fau-fablab/uacs-hardware/pcb/uacs.sch

## EAGLE design pcb/uacs.sch (2014-12-10)

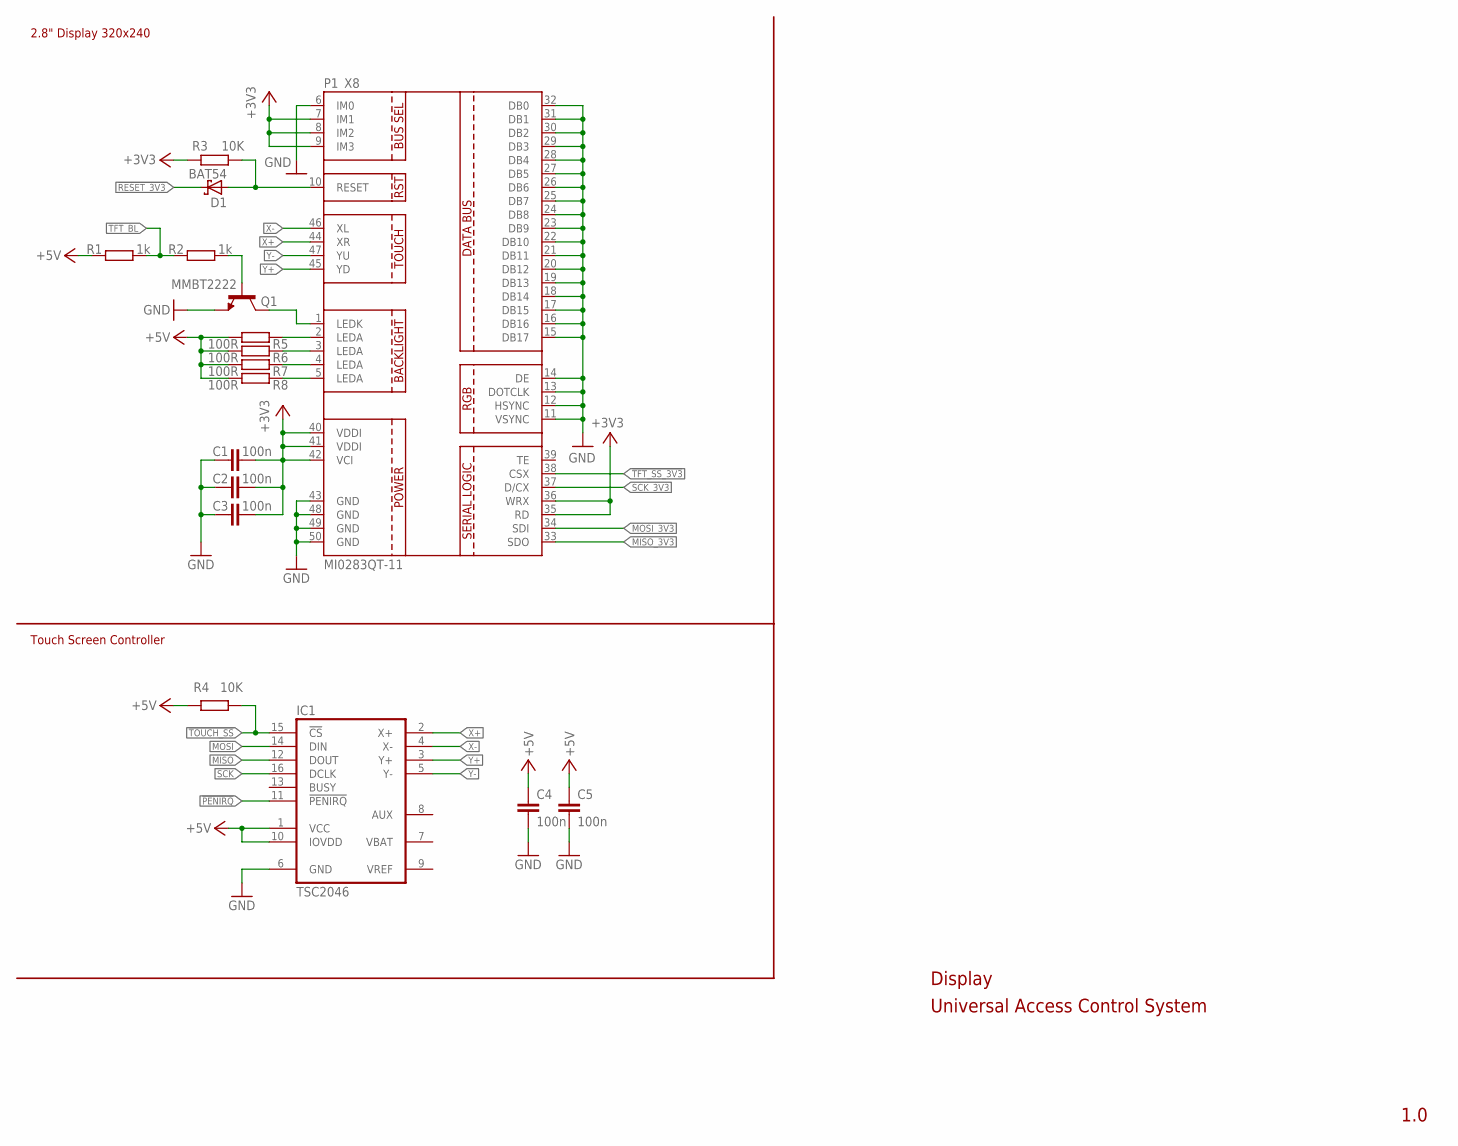
[picture p12: schematic uacs.sch, sheet 1]

Parts:
C1, C2, C3, C4, C5: 100n; C0603
D1: BAT54; SOT23
IC1: TSC2046; TSSOP16
P1: MI0283QT-11
Q1: MMBT2222; SOT23-3
R1, R2: 1k; R0603
R3, R4: 10K; R0603
R5, R6, R7, R8: 100R; R0603

Connections:
!PENIRQ: IC1.11 (!PENIRQ)
!RESET_3V3: D1.3 (C)
!TFT_SS_3V3: P1.38 (CSX)
!TOUCH_SS: IC1.15 (!CS), R4.1
+3V3: C1.2, C2.2, C3.2, P1.7 (IM1), P1.8 (IM2), P1.9 (IM3), P1.35 (RD), P1.36 (WRX), P1.40 (VDDI), P1.41 (VDDI), P1.42 (VCI), R3.2
+5V: C4.1, C5.1, IC1.1 (VCC), IC1.10 (IOVDD), R1.1, R4.2, R5.2, R6.2, R7.2, R8.2
GND: C1.1, C2.1, C3.1, C4.2, C5.2, IC1.6 (GND), P1.6 (IM0), P1.11 (VSYNC), P1.12 (HSYNC), P1.13 (DOTCLK), P1.14 (DE), P1.15 (DB17), P1.16 (DB16), P1.17 (DB15), P1.18 (DB14), P1.19 (DB13), P1.20 (DB12), P1.21 (DB11), P1.22 (DB10), P1.23 (DB9), P1.24 (DB8), P1.25 (DB7), P1.26 (DB6), P1.27 (DB5), P1.28 (DB4), P1.29 (DB3), P1.30 (DB2), P1.31 (DB1), P1.32 (DB0), P1.43 (GND), P1.48 (GND), P1.49 (GND), P1.50 (GND), Q1.2 (E)
MISO: IC1.12 (DOUT)
MISO_3V3: P1.33 (SDO)
MOSI: IC1.14 (DIN)
MOSI_3V3: P1.34 (SDI)
unnamed: P1.1 (LEDK), Q1.3 (C)
unnamed: P1.5 (LEDA), R8.1
unnamed: Q1.1 (B), R2.2
unnamed: P1.4 (LEDA), R7.1
unnamed: P1.3 (LEDA), R6.1
unnamed: P1.2 (LEDA), R5.1
unnamed: D1.1 (A), P1.10 (RESET), R3.1
SCK: IC1.16 (DCLK)
SCK_3V3: P1.37 (D/CX)
TFT_BL: R1.2, R2.1
X+: IC1.2 (X+), P1.44 (XR)
X-: IC1.4 (X-), P1.46 (XL)
Y+: IC1.3 (Y+), P1.45 (YD)
Y-: IC1.5 (Y-), P1.47 (YU)

Notes on the sheet:
2.8" Display 320x240
Touch Screen Controller
Display
1.0
Universal Access Control System

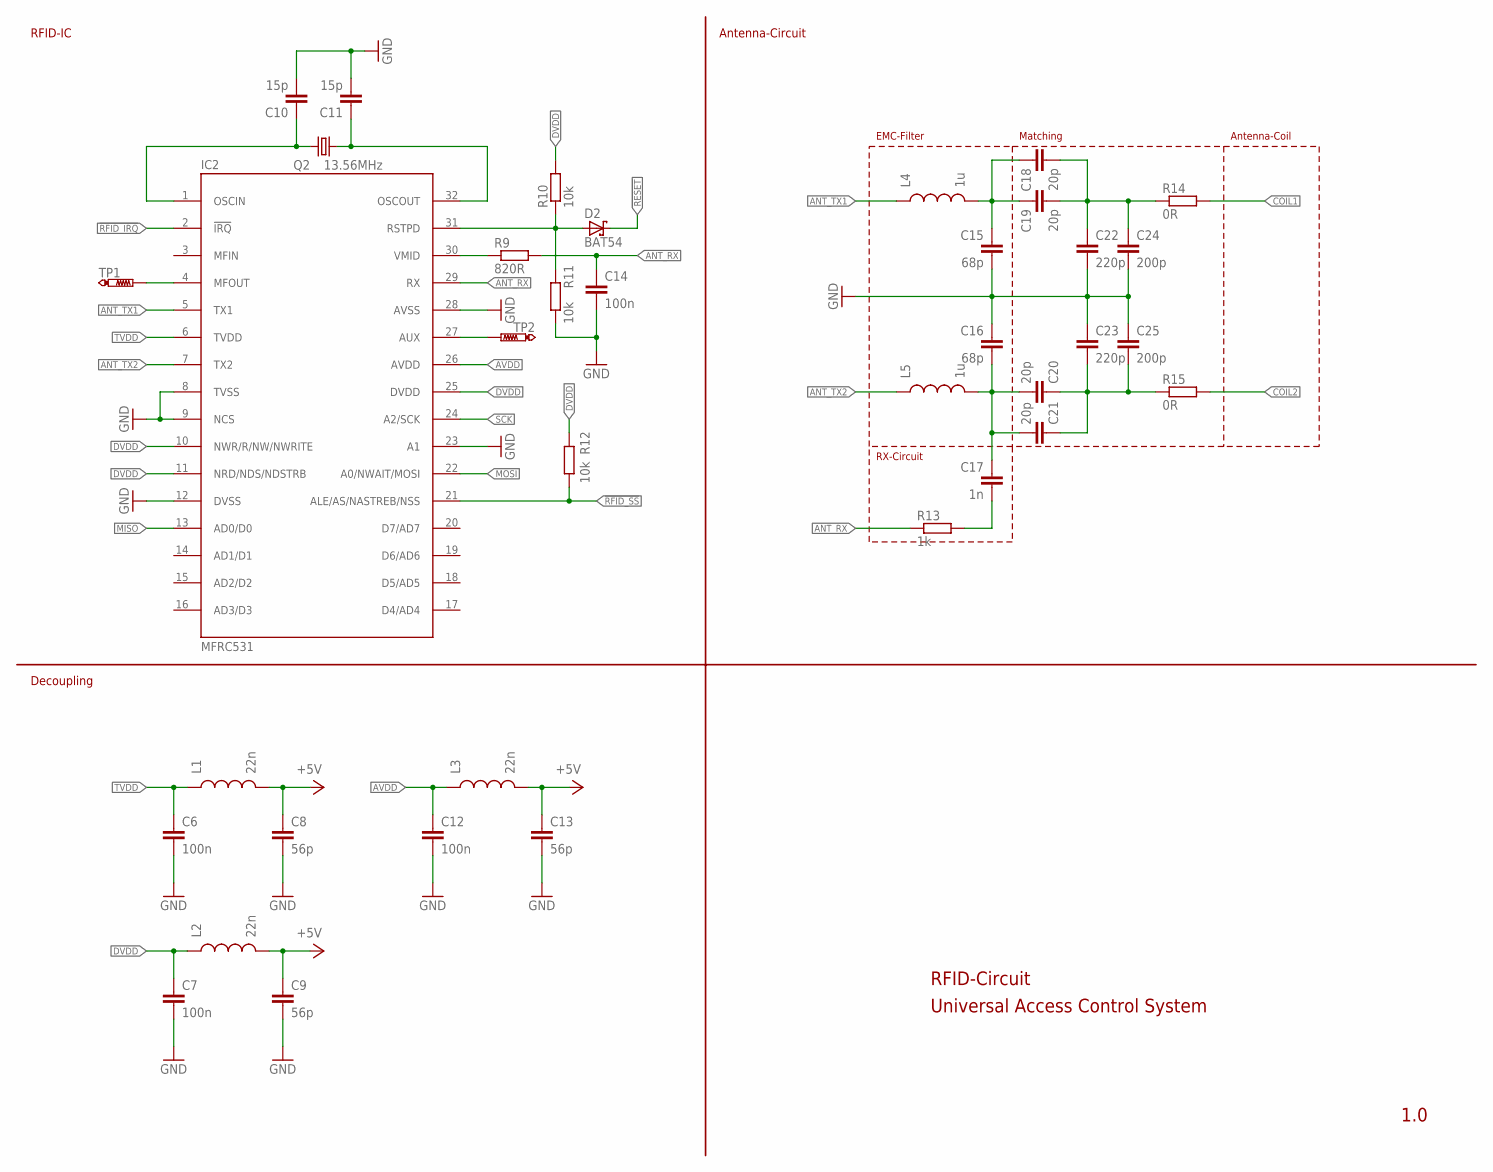
[picture p13: schematic uacs.sch, sheet 2]

Parts:
C6, C7, C12, C14: 100n; C0603
C8, C9, C13: 56p; C0603
C10, C11: 15p; C0603
C15, C16: 68p; C0603
C17: 1n; C0603
C18, C19, C20, C21: 20p; C0603
C22, C23: 220p; C0603
C24, C25: 200p; C0603
D2: BAT54; SOT23
IC2: MFRC531; SO32
L1, L2, L3: 22n; 0603
L4, L5: 1u; 0603
Q2: 13.56MHz; SM49
R9: 820R; R0603
R10, R11, R12: 10k; R0603
R13: 1k; R0603
R14, R15: 0R; R0603
TP1, TP2: PTR1B1,27; B1,27

Connections:
!RESET: D2.3 (C)
!RFID_IRQ: IC2.2 (!IRQ)
!RFID_SS: IC2.21 (ALE/AS/NASTREB/NSS), R12.1
+5V: C8.1, C9.1, C13.1, L1.2, L2.2, L3.2
ANT_RX: C14.1, IC2.29 (RX), R9.2, R13.1
ANT_TX1: IC2.5 (TX1), L4.1
ANT_TX2: IC2.7 (TX2), L5.1
AVDD: C12.1, IC2.26 (AVDD), L3.1
COIL1: R14.2
COIL2: R15.2
DVDD: C7.1, IC2.10 (NWR/R/NW/NWRITE), IC2.11 (NRD/NDS/NDSTRB), IC2.25 (DVDD), L2.1, R10.2, R12.2
GND: C6.2, C7.2, C8.2, C9.2, C10.2, C11.2, C12.2, C13.2, C14.2, C15.2, C16.1, C22.2, C23.1, C24.2, C25.1, IC2.8 (TVSS), IC2.9 (NCS), IC2.12 (DVSS), IC2.23 (A1), IC2.28 (AVSS), R11.1
MISO: IC2.13 (AD0/D0)
MOSI: IC2.22 (A0/NWAIT/MOSI)
unnamed: D2.1 (A), IC2.31 (RSTPD), R10.1, R11.2
unnamed: C11.1, IC2.32 (OSCOUT), Q2.1
unnamed: IC2.4 (MFOUT), TP1.TP
unnamed: IC2.30 (VMID), R9.1
unnamed: IC2.27 (AUX), TP2.TP
unnamed: C16.2, C17.1, C20.2, C21.2, L5.2
unnamed: C17.2, R13.2
unnamed: C15.1, C18.1, C19.1, L4.2
unnamed: C18.2, C19.2, C22.1, C24.1, R14.1
unnamed: C20.1, C21.1, C23.2, C25.2, R15.1
unnamed: C10.1, IC2.1 (OSCIN), Q2.2
SCK: IC2.24 (A2/SCK)
TVDD: C6.1, IC2.6 (TVDD), L1.1

Notes on the sheet:
EMC-Filter
Matching
RX-Circuit
Antenna-Coil
RFID-IC
Antenna-Circuit
Decoupling
RFID-Circuit
1.0
Universal Access Control System

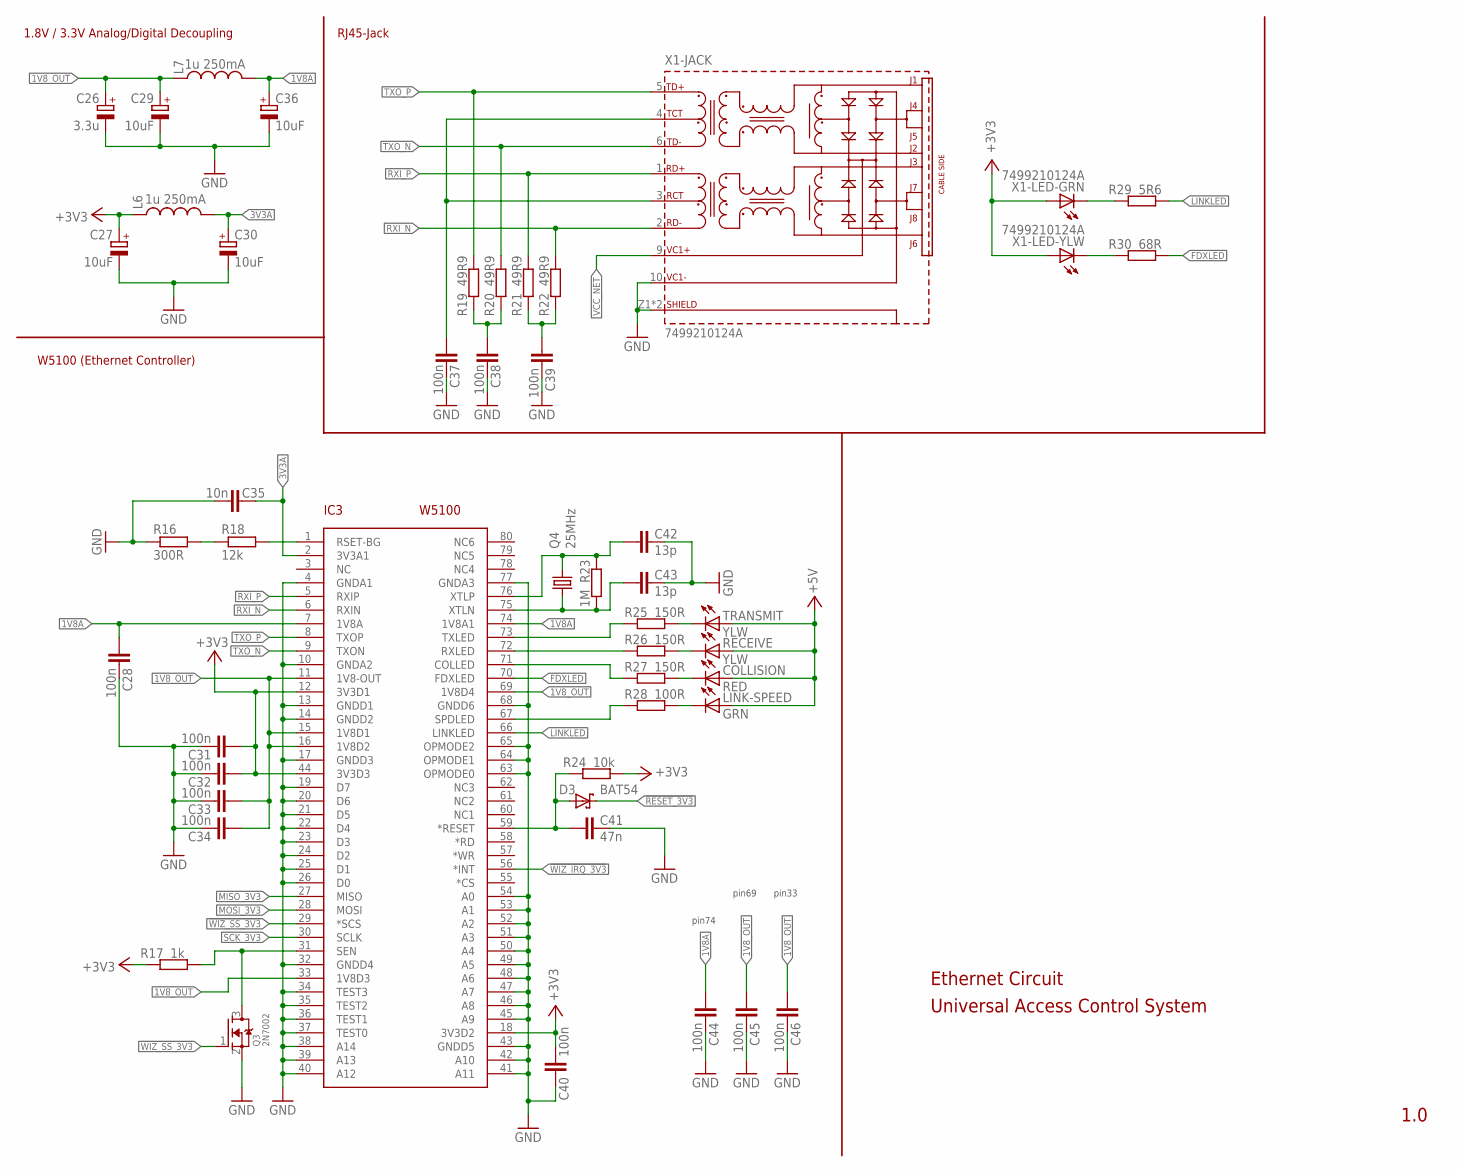
[picture p14: schematic uacs.sch, sheet 3]

Parts:
C26: 3.3u; B/3528-21R
C27, C29, C30, C36: 10uF; B/3528-21R
C28, C31, C32, C33, C34, C37, C38, C39, C40, C44, C45, C46: 100n; C0603
C35: 10n; C0603
C41: 47n; C0603
C42, C43: 13p; C0603
COLLISION: RED; CHIPLED_0603
D3: BAT54; SOT23
IC3: W5100; SQFP-S-10X10-80
L6, L7: 1u 250mA; 0603
LINK-SPEED: GRN; CHIPLED_0603
Q3: 2N7002; SOT23
Q4: 25MHz; SM49
R16: 300R; R0603
R17: 1k; R0603
R18: 12k; R0603
R19, R20, R21, R22: 49R9; R0603
R23: 1M; R0603
R24: 10k; R0603
R25, R26, R27: 150R; R0603
R28: 100R; R0603
R29: 5R6; R0603
R30: 68R; R0603
RECEIVE: YLW; CHIPLED_0603
TRANSMIT: YLW; CHIPLED_0603
X1: 7499210124A

Connections:
1V8A: C28.1, C36.+, C44.1, IC3.7 (1V8A), IC3.74 (1V8A1), L7.2
1V8_OUT: C26.+, C29.+, C33.1, C34.1, C45.1, C46.1, IC3.11 (1V8-OUT), IC3.15 (1V8D1), IC3.16 (1V8D2), IC3.33 (1V8D3), IC3.69 (1V8D4), L7.1
3V3A: C30.+, C35.1, IC3.2 (3V3A1), L6.2
!RESET_3V3: D3.3 (C)
!WIZ_IRQ_3V3: IC3.56 (*INT)
!WIZ_SS_3V3: IC3.29 (*SCS), Q3.1 (G)
+3V3: C27.+, C31.1, C32.1, C40.1, IC3.12 (3V3D1), IC3.18 (3V3D2), IC3.44 (3V3D3), L6.1, R17.1, R24.2, X1.12 (A), X1.14 (A)
+5V: COLLISION.A, LINK-SPEED.A, RECEIVE.A, TRANSMIT.A
FDXLED: IC3.70 (FDXLED), R30.2
GND: C26.-, C27.-, C28.2, C29.-, C30.-, C31.2, C32.2, C33.2, C34.2, C35.2, C36.-, C37.2, C38.2, C39.2, C40.2, C41.2, C42.2, C43.2, C44.2, C45.2, C46.2, IC3.4 (GNDA1), IC3.10 (GNDA2), IC3.13 (GNDD1), IC3.14 (GNDD2), IC3.17 (GNDD3), IC3.19 (D7), IC3.20 (D6), IC3.21 (D5), IC3.22 (D4), IC3.23 (D3), IC3.24 (D2), IC3.25 (D1), IC3.26 (D0), IC3.32 (GNDD4), IC3.34 (TEST3), IC3.35 (TEST2), IC3.36 (TEST1), IC3.37 (TEST0), IC3.38 (A14), IC3.39 (A13), IC3.40 (A12), IC3.41 (A11), IC3.42 (A10), IC3.43 (GNDD5), IC3.45 (A9), IC3.46 (A8), IC3.47 (A7), IC3.48 (A6), IC3.49 (A5), IC3.50 (A4), IC3.51 (A3), IC3.52 (A2), IC3.53 (A1), IC3.54 (A0), IC3.63 (OPMODE0), IC3.64 (OPMODE1), IC3.65 (OPMODE2), IC3.68 (GNDD6), IC3.77 (GNDA3), Q3.2 (S), R16.1, X1.10 (VC1-), X1.Z1 (SHIELD)
LINKLED: IC3.66 (LINKLED), R29.2
MISO_3V3: IC3.27 (MISO)
MOSI_3V3: IC3.28 (MOSI)
unnamed: IC3.1 (RSET-BG), R18.2
unnamed: R30.1, X1.13 (C)
unnamed: R29.1, X1.11 (C)
unnamed: C41.1, D3.1 (A), IC3.59 (*RESET), R24.1
unnamed: C39.1, R21.1, R22.1
unnamed: R25.2, TRANSMIT.C
unnamed: C38.1, R19.1, R20.1
unnamed: IC3.67 (SPDLED), R28.1
unnamed: R26.2, RECEIVE.C
unnamed: IC3.71 (COLLED), R27.1
unnamed: IC3.72 (RXLED), R26.1
unnamed: IC3.73 (TXLED), R25.1
unnamed: COLLISION.C, R27.2
unnamed: LINK-SPEED.C, R28.2
unnamed: C43.1, IC3.75 (XTLN), Q4.1, R23.1
unnamed: C42.1, IC3.76 (XTLP), Q4.2, R23.2
unnamed: R16.2, R18.1
RXI_N: IC3.6 (RXIN), R22.2, X1.2 (RD-)
RXI_P: IC3.5 (RXIP), R21.2, X1.1 (RD+)
SCK_3V3: IC3.30 (SCLK)
SEN: IC3.31 (SEN), Q3.3 (D), R17.2
TXCT: C37.1, X1.3 (RCT), X1.4 (TCT)
TXO_N: IC3.9 (TXON), R20.2, X1.6 (TD-)
TXO_P: IC3.8 (TXOP), R19.2, X1.5 (TD+)
VCC_NET: X1.9 (VC1+)

Notes on the sheet:
1.8V / 3.3V Analog/Digital Decoupling
RJ45-Jack
W5100 (Ethernet Controller)
Ethernet Circuit
1.0
pin74
pin69
pin33
Universal Access Control System

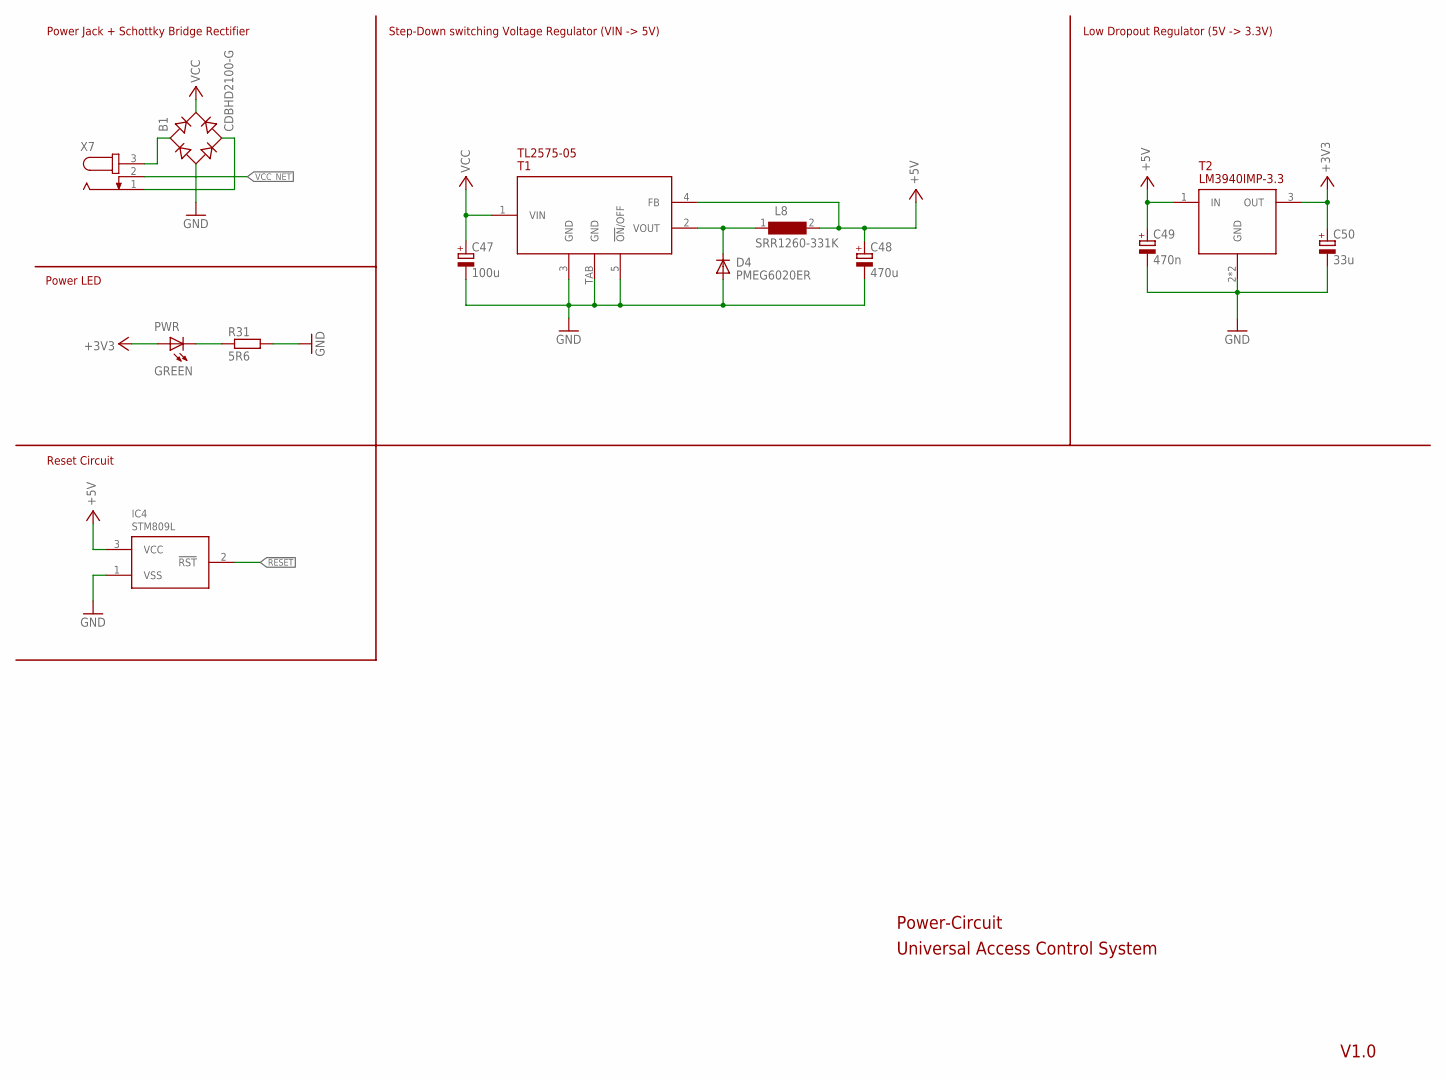
[picture p15: schematic uacs.sch, sheet 4]

Parts:
B1: CDBHD2100-G; MBS
C47: 100u; PANASONIC_G
C48: 470u; PANASONIC_G
C49: 470n; PANASONIC_B
C50: 33u; PANASONIC_D
D4: PMEG6020ER; SOD-123
IC4: STM809L; SOT-23-3
L8: SRR1260-331K; WE-PD_1260/1245/1280/1210
PWR: GREEN; CHIPLED_0603
R31: 5R6; R0603
T1: TL2575-05; TO-263-5
T2: LM3940IMP-3.3; SOT223
X7: JACK-PLUG1; SPC4078

Connections:
!RESET: IC4.2 (!RST)
+3V3: C50.+, PWR.A, T2.3 (OUT)
+5V: C48.+, C49.+, IC4.3 (VCC), L8.2, T1.4 (FB), T2.1 (IN)
GND: B1.-, C47.-, C48.-, C49.-, C50.-, D4.A, IC4.1 (VSS), R31.2, T1.3 (GND), T1.5 (!ON!/OFF), T1.TAB (GND), T2.2 (GND)
unnamed: PWR.C, R31.1
unnamed: B1.AC1, X7.3
unnamed: B1.AC2, X7.1
unnamed: D4.C, L8.1, T1.2 (VOUT)
VCC: B1.+, C47.+, T1.1 (VIN)
VCC_NET: X7.2

Notes on the sheet:
Power Jack + Schottky Bridge Rectifier
Step-Down switching Voltage Regulator (VIN -> 5V)
Low Dropout Regulator (5V -> 3.3V)
Power-Circuit
V1.0
Power LED
Reset Circuit
Universal Access Control System

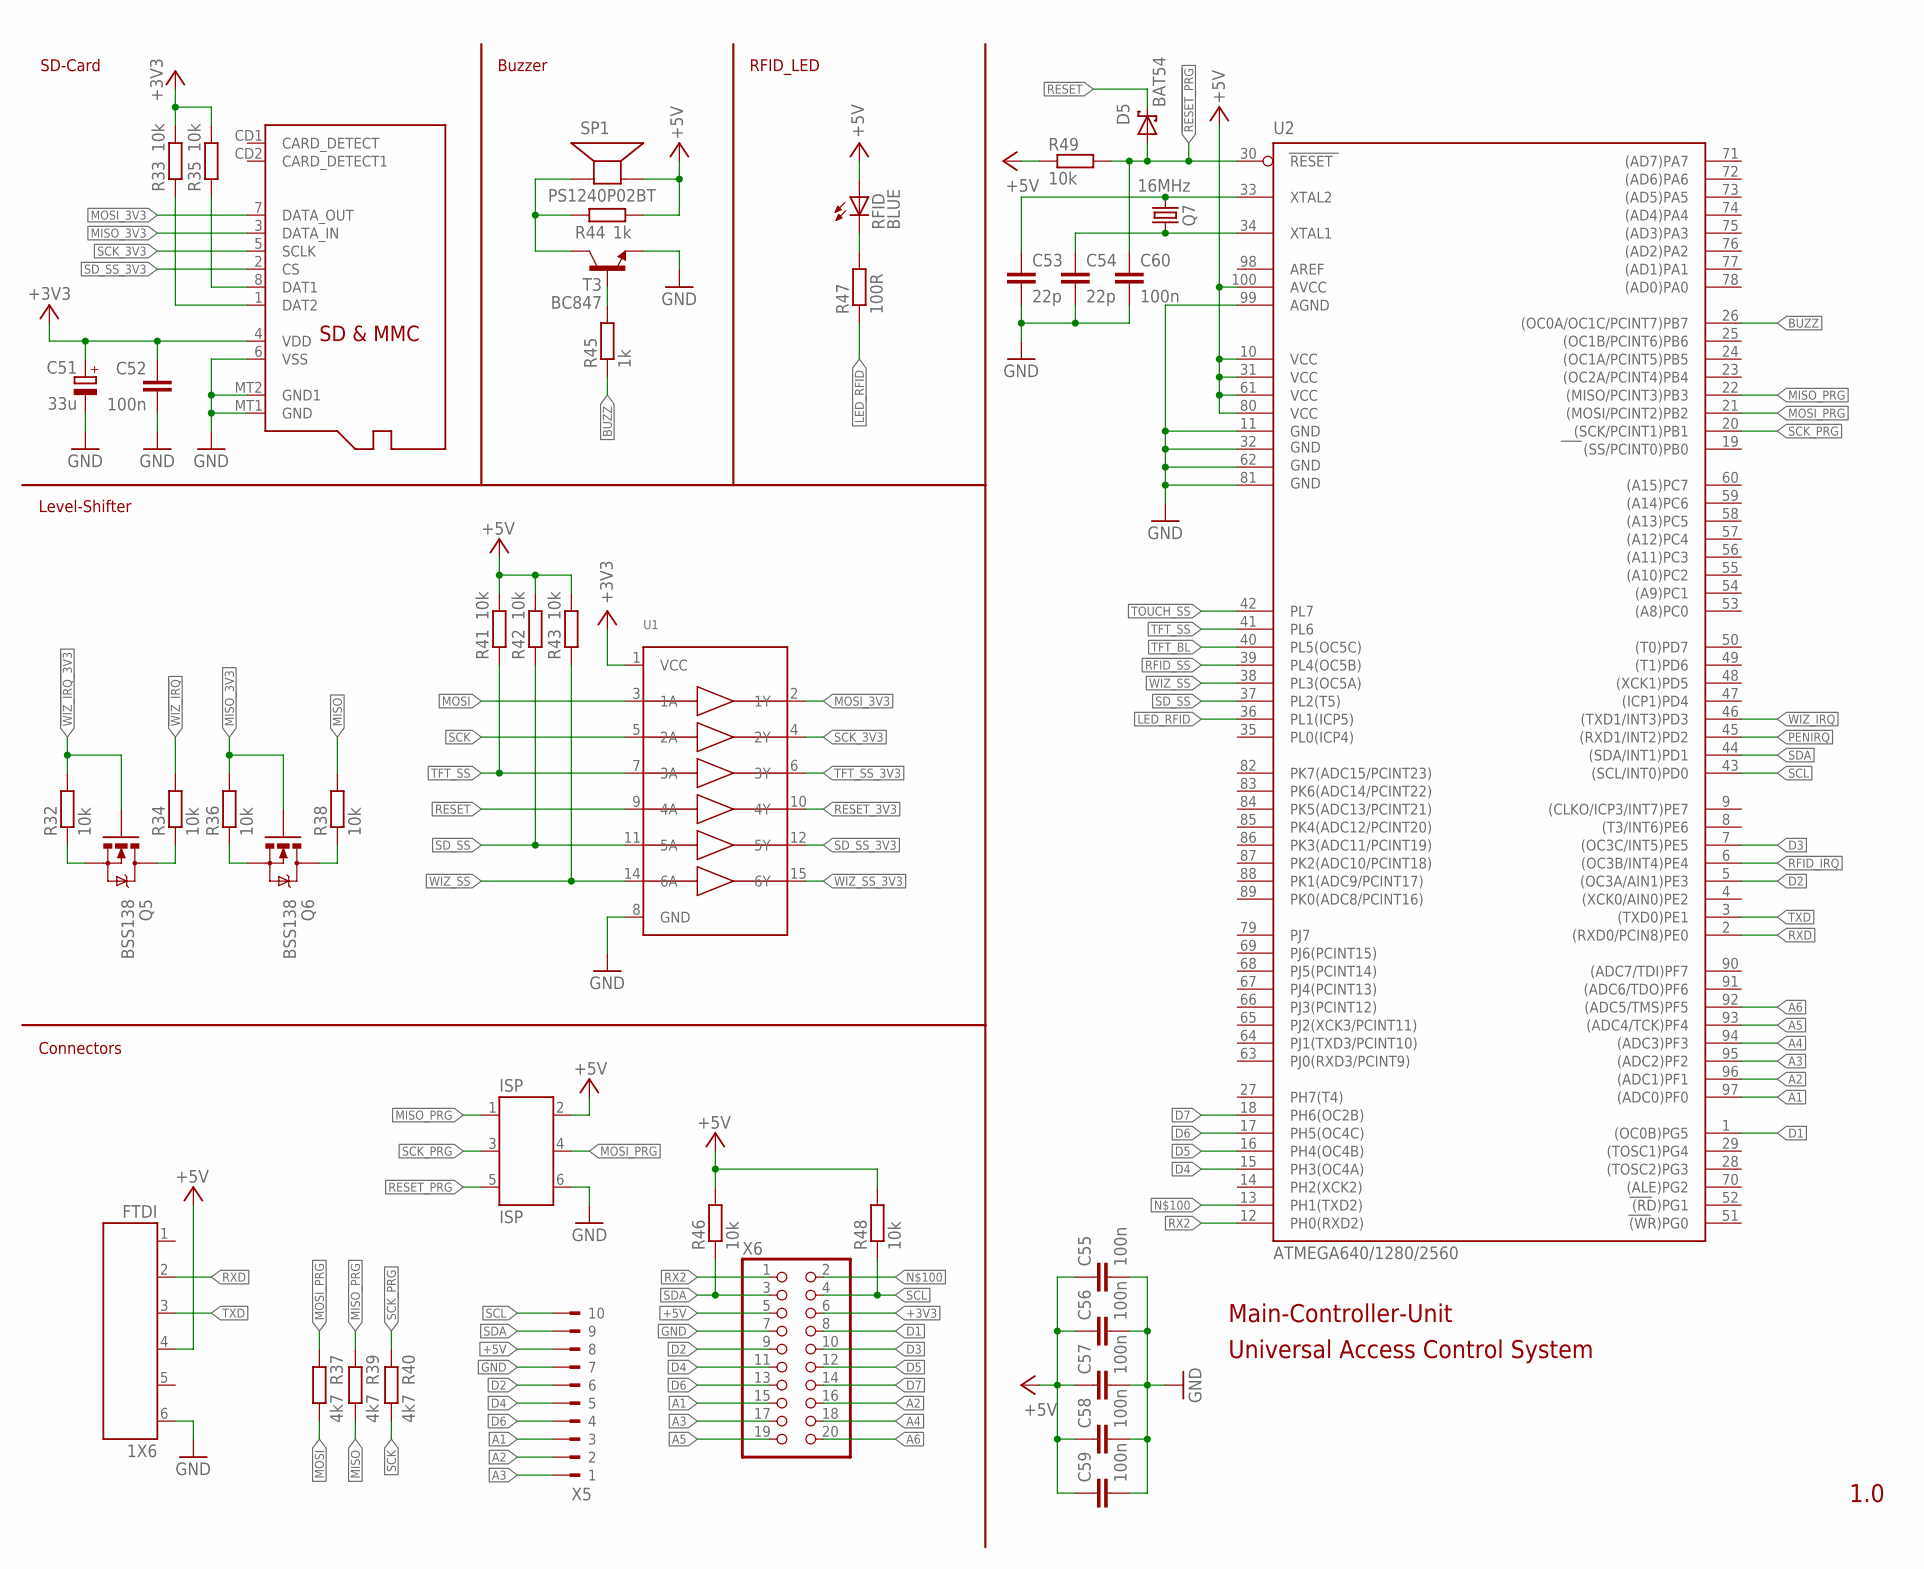
[picture p16: schematic uacs.sch, sheet 5]

Parts:
C51: 33u; C/6032-28R
C52, C55, C56, C57, C58, C59, C60: 100n; C0603
C53, C54: 22p; C0603
D5: BAT54; SOT23
FTDI: 1X6
ISP: ISP; 2X3
Q5, Q6: BSS138; SOT23
Q7: 16MHz; SM49
R32, R33, R34, R35, R36, R38, R41, R42, R43, R46, R48, R49: 10k; R0603
R37, R39, R40: 4k7; R0603
R44, R45: 1k; R0603
R47: 100R; R0603
RFID: BLUE; CHIPLED_0603
SP1: PS1240P02BT; PS12
T3: BC847; SOT23
U1: 74HC4050DTSSOP; TSSOP16
U2: ATMEGA640/1280/2560; TQFP100
X3: MICROSD
X5: 180-10
X6: PINHD-2X10; 2X10

Connections:
!PENIRQ: U2.45 ((RXD1/INT2)PD2)
!RESET: D5.3 (C), U1.9 (4A)
!RESET_3V3: U1.10 (4Y)
!RESET_PRG: C60.1, D5.1 (A), ISP.5, R49.2, U2.30 (RESET)
!RFID_IRQ: U2.6 ((OC3B/INT4)PE4)
!RFID_SS: U2.39 (PL4(OC5B))
!SD_SS: R42.1, U1.11 (5A), U2.37 (PL2(T5))
!SD_SS_3V3: U1.12 (5Y), X3.2 (CS)
!TFT_SS: R41.1, U1.7 (3A), U2.41 (PL6)
!TFT_SS_3V3: U1.6 (3Y)
!TOUCH_SS: U2.42 (PL7)
!WIZ_IRQ: R34.2, U2.46 ((TXD1/INT3)PD3)
!WIZ_IRQ_3V3: Q5.1 (G), R32.2
!WIZ_SS: R43.1, U1.14 (6A), U2.38 (PL3(OC5A))
!WIZ_SS_3V3: U1.15 (6Y)
+3V3: C51.+, C52.1, R33.2, R35.2, U1.1 (VCC), X3.4 (VDD), X6.6
+5V: C55.1, C56.1, C57.1, C58.1, C59.1, FTDI.4, ISP.2, R41.2, R42.2, R43.2, R44.2, R46.2, R48.2, R49.1, RFID.A, SP1.P$2 (-), U2.10 (VCC), U2.31 (VCC1), U2.61 (VCC2), U2.80 (VCC3), U2.100 (AVCC), X5.8, X6.5
A1: U2.97 ((ADC0)PF0), X5.3, X6.15
A2: U2.96 ((ADC1)PF1), X5.2, X6.16
A3: U2.95 ((ADC2)PF2), X5.1, X6.17
A4: U2.94 ((ADC3)PF3), X6.18
A5: U2.93 ((ADC4/TCK)PF4), X6.19
A6: U2.92 ((ADC5/TMS)PF5), X6.20
BUZZ: R45.1, U2.26 ((OC0A/OC1C/PCINT7)PB7)
D1: U2.1 ((OC0B)PG5), X6.8
D2: U2.5 ((OC3A/AIN1)PE3), X5.6, X6.9
D3: U2.7 ((OC3C/INT5)PE5), X6.10
D4: U2.15 (PH3(OC4A)), X5.5, X6.11
D5: U2.16 (PH4(OC4B)), X6.12
D6: U2.17 (PH5(OC4C)), X5.4, X6.13
D7: U2.18 (PH6(OC2B)), X6.14
GND: C51.-, C52.2, C53.2, C54.2, C55.2, C56.2, C57.2, C58.2, C59.2, C60.2, FTDI.6, ISP.6, T3.2 (E), U1.8 (GND), U2.11 (GND), U2.32 (GND1), U2.62 (GND2), U2.81 (GND3), U2.99 (AGND), X3.6 (VSS), X3.MT1 (GND), X3.MT2 (GND1), X5.7, X6.7
LED_RFID: R47.1, U2.36 (PL1(ICP5))
MISO: R38.2, R39.2
MISO_3V3: Q6.1 (G), R36.2, X3.3 (DATA_IN)
MISO_PRG: ISP.1, R39.1, U2.22 ((MISO/PCINT3)PB3)
MOSI: R37.2, U1.3 (1A)
MOSI_3V3: U1.2 (1Y), X3.7 (DATA_OUT)
MOSI_PRG: ISP.4, R37.1, U2.21 ((MOSI/PCINT2)PB2)
unnamed: R47.2, RFID.C
unnamed: C54.1, Q7.1, U2.34 (XTAL1)
unnamed: C53.1, Q7.2, U2.33 (XTAL2)
unnamed: R35.1, X3.8 (DAT1)
unnamed: R44.1, SP1.P$1 (+), T3.3 (C)
unnamed: R45.2, T3.1 (B)
unnamed: Q6.3 (D), R38.1
unnamed: Q6.2 (S), R36.1
unnamed: Q5.2 (S), R32.1
unnamed: Q5.3 (D), R34.1
unnamed: R33.1, X3.1 (DAT2)
unnamed: U2.13 (PH1(TXD2)), X6.2
RX2: U2.12 (PH0(RXD2)), X6.1
RXD: FTDI.2, U2.2 ((RXD0/PCIN8)PE0)
SCK: R40.2, U1.5 (2A)
SCK_3V3: U1.4 (2Y), X3.5 (SCLK)
SCK_PRG: ISP.3, R40.1, U2.20 ((SCK/PCINT1)PB1)
SCL: R48.1, U2.43 ((SCL/INT0)PD0), X5.10, X6.4
SDA: R46.1, U2.44 ((SDA/INT1)PD1), X5.9, X6.3
TFT_BL: U2.40 (PL5(OC5C))
TXD: FTDI.3, U2.3 ((TXD0)PE1)

Notes on the sheet:
Main-Controller-Unit
1.0
SD-Card
Buzzer
Level-Shifter
RFID_LED
Connectors
Universal Access Control System
