fau-fablab/uacs-hardware/pcb/top/uacs-2-top-rfid.sch

## KiCad design pcb/top/uacs-2-top-rfid.sch (2015-04-09)

Schematic: uacs-2-top-rfid.sch

Parts:
C1, C2, C3, C4, C5, C6, C7, C8: na
C9, C10: 220p
C11, C15, C16, C18, C19, C20, C23, C24, C26, C28, C29: 100n
C12: 1n
C13, C14, C21, C25: 22p
C17, C22, C27: 10u
IC1: ATMEGA328P-A; TQFP32
IC2: PN532
L1, L2: 560n
L3, L4: FERRIT
P2: ISP
R1, R2: na
R3: 2.7k
R4: 10k
R5: 1k
R6: 47k
X1: 8M
X2: 27.12M

Notes on the sheet:
testpoint
EMC-Filter
Matching
power-on-reset fähig!
rfid-ic
rfid power decoupling
TODO: design 13.56MHz antenna
config for spi operation
nc (section 8.4.2)
host interface supply
main power supply
see section 13
remark: choose a low esr (x5r/x7r) version for all 10u caps
floating AN153710 2.1.1/2.1.2
remark: use C0G caps
rfid mcu
